DJFliX/OakPowerBoard/code/oakpowerboard/roboto_10.h

#ifndef __ROBOTO_10_
#define __ROBOTO_10_

const char Roboto_Plain_10[] PROGMEM = {
  0x0A, // Width: 10
  0x0D, // Height: 13
  0x20, // First Char: 32
  0xE0, // Numbers of Chars: 224

  // Char Widths:
  0x02, // 32: 2
  0x03, // 33: 3
  0x04, // 34: 4
  0x06, // 35: 6
  0x07, // 36: 7
  0x09, // 37: 9
  0x07, // 38: 7
  0x03, // 39: 3
  0x04, // 40: 4
  0x04, // 41: 4
  0x05, // 42: 5
  0x05, // 43: 5
  0x03, // 44: 3
  0x03, // 45: 3
  0x03, // 46: 3
  0x04, // 47: 4
  0x07, // 48: 7
  0x06, // 49: 6
  0x06, // 50: 6
  0x06, // 51: 6
  0x06, // 52: 6
  0x06, // 53: 6
  0x07, // 54: 7
  0x06, // 55: 6
  0x06, // 56: 6
  0x07, // 57: 7
  0x02, // 58: 2
  0x03, // 59: 3
  0x06, // 60: 6
  0x05, // 61: 5
  0x06, // 62: 6
  0x06, // 63: 6
  0x0A, // 64: 10
  0x07, // 65: 7
  0x07, // 66: 7
  0x07, // 67: 7
  0x07, // 68: 7
  0x06, // 69: 6
  0x06, // 70: 6
  0x08, // 71: 8
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

  // Font Data:
  0x00,0x00,0x00,0x00, // 32
  0x80,0x24,0x09,0x10,0x00, // 33
  0x00,0x66,0x00,0x00,0x00,0x00,0x00, // 34
  0x00,0x40,0x51,0x3E,0x45,0xF9,0x8A,0x02,0x00,0x00, // 35
  0x00,0x04,0x47,0x24,0x22,0x60,0x40,0x22,0x0E,0x02,0x00,0x00, // 36
  0x00,0x00,0x38,0x50,0xA1,0xC2,0x03,0x1A,0x4C,0x94,0xC0,0x00,0x00,0x00,0x00, // 37
  0x00,0x00,0x87,0x42,0x61,0x30,0x64,0x12,0x1E,0x00,0x00,0x00, // 38
  0x80,0x04,0x00,0x00,0x00, // 39
  0x80,0x24,0x22,0x22,0x22,0x44,0x08, // 40
  0x10,0x22,0x44,0x44,0x44,0x22,0x01, // 41
  0x00,0x90,0xE2,0x14,0x02,0x00,0x00,0x00,0x00, // 42
  0x00,0x00,0x42,0xC8,0x27,0x04,0x00,0x00,0x00, // 43
  0x00,0x00,0x00,0x90,0x00, // 44
  0x00,0x00,0x1C,0x00,0x00, // 45
  0x00,0x00,0x00,0x10,0x00, // 46
  0x00,0x48,0x44,0x22,0x12,0x01,0x00, // 47
  0x00,0x00,0x47,0x24,0x12,0x89,0x44,0x22,0x0E,0x00,0x00,0x00, // 48
  0x00,0x80,0x38,0x08,0x82,0x20,0x08,0x02,0x00,0x00, // 49
  0x00,0xC0,0x48,0x12,0x84,0x10,0x86,0x07,0x00,0x00, // 50
  0x00,0xC0,0x48,0x10,0x03,0x41,0x12,0x03,0x00,0x00, // 51
  0x00,0x00,0x61,0x14,0x25,0xF9,0x10,0x04,0x00,0x00, // 52
  0x00,0xE0,0x09,0x82,0x03,0x41,0x92,0x03,0x00,0x00, // 53
  0x00,0x00,0x86,0x20,0xF0,0x88,0x44,0x22,0x0E,0x00,0x00,0x00, // 54
  0x00,0xF0,0x41,0x08,0x42,0x10,0x84,0x00,0x00,0x00, // 55
  0x00,0xC0,0x48,0x12,0x23,0x49,0x12,0x03,0x00,0x00, // 56
  0x00,0x00,0x47,0x24,0x12,0xF1,0x40,0x10,0x06,0x00,0x00,0x00, // 57
  0x00,0x02,0x08,0x00, // 58
  0x00,0x20,0x00,0x92,0x00, // 59
  0x00,0x00,0x00,0x10,0x23,0x30,0x10,0x00,0x00,0x00, // 60
  0x00,0x00,0x00,0x3C,0xF0,0x00,0x00,0x00,0x00, // 61
  0x00,0x00,0x00,0x02,0x03,0x31,0x02,0x00,0x00,0x00, // 62
  0x00,0xE0,0x48,0x10,0xC6,0x10,0x00,0x01,0x00,0x00, // 63
  0x00,0x00,0x80,0x07,0x21,0x34,0xA9,0xA4,0x92,0x4A,0x2A,0x69,0x43,0x00,0x0E,0x00,0x00, // 64
  0x00,0x00,0x82,0x41,0xA1,0x48,0x7C,0xA2,0x10,0x00,0x00,0x00, // 65
  0x00,0x80,0x47,0x24,0xF2,0x88,0x44,0x22,0x0F,0x00,0x00,0x00, // 66
  0x00,0x00,0xC7,0x24,0x14,0x08,0x84,0x26,0x0E,0x00,0x00,0x00, // 67
  0x00,0x80,0x47,0x22,0x12,0x89,0x44,0x12,0x0F,0x00,0x00,0x00, // 68
  0x00,0xE0,0x0B,0x82,0x27,0x08,0x82,0x0F,0x00,0x00, // 69
  0x00,0xE0,0x09,0x82,0xE0,0x09,0x82,0x00,0x00,0x00, // 70
  0x00,0x00,0x3C,0x66,0x02,0x02,0x72,0x42,0x44,0x3C,0x00,0x00,0x00,0x00, // 71
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
};

#endif
