DJFliX/OakPowerBoard/code/oakpowerboard/roboto_thin_20.h

#ifndef __ROBOTO_20_
#define __ROBOTO_20_

const char Roboto_Thin_Plain_20[] PROGMEM = {
  0x13, // Width: 19
  0x18, // Height: 24
  0x20, // First Char: 32
  0xE0, // Numbers of Chars: 224

  // Char Widths:
  0x05, // 32: 5
  0x03, // 33: 3
  0x05, // 34: 5
  0x0B, // 35: 11
  0x0B, // 36: 11
  0x0F, // 37: 15
  0x0C, // 38: 12
  0x03, // 39: 3
  0x06, // 40: 6
  0x06, // 41: 6
  0x09, // 42: 9
  0x0B, // 43: 11
  0x03, // 44: 3
  0x06, // 45: 6
  0x04, // 46: 4
  0x08, // 47: 8
  0x0B, // 48: 11
  0x0B, // 49: 11
  0x0B, // 50: 11
  0x0B, // 51: 11
  0x0C, // 52: 12
  0x0B, // 53: 11
  0x0B, // 54: 11
  0x0B, // 55: 11
  0x0C, // 56: 12
  0x0B, // 57: 11
  0x04, // 58: 4
  0x03, // 59: 3
  0x0A, // 60: 10
  0x0B, // 61: 11
  0x0A, // 62: 10
  0x09, // 63: 9
  0x13, // 64: 19
  0x0C, // 65: 12
  0x0D, // 66: 13
  0x0D, // 67: 13
  0x0D, // 68: 13
  0x0C, // 69: 12
  0x0C, // 70: 12
  0x0E, // 71: 14
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

  // Font Data:
  0x00,0x00,0x00,0x00,0x00,0x00,0x00,0x00,0x00,0x00,0x00,0x00,0x00,0x00,0x00,0x00, // 32
  0x00,0x20,0x49,0x92,0x24,0x09,0x80,0x00,0x00,0x00, // 33
  0x00,0x00,0xA0,0x94,0x52,0x00,0x00,0x00,0x00,0x00,0x00,0x00,0x00,0x00,0x00,0x00, // 34
  0x00,0x00,0x00,0x00,0x00,0x00,0x21,0x88,0x40,0x04,0x22,0xFE,0x87,0x08,0x42,0x10,0x81,0x08,0x44,0xFC,0x1F,0x11,0x84,0x20,0x02,0x11,0x00,0x00,0x00,0x00,0x00,0x00,0x00,0x00, // 35
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
  0x00,0x00,0x00,0x00,0x00,0x00,0x00,0xF0,0x01,0x82,0x41,0x40,0x08,0x20,0x02,0x80,0x00,0x20,0x00,0x08,0x00,0x82,0x8F,0x00,0x22,0x80,0x08,0x20,0x04,0x08,0x02,0x02,0x7F,0x00,0x00,0x00,0x00,0x00,0x00,0x00,0x00,0x00,0x00, // 71
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
};
#endif
