DJFliX/OakPowerBoard/code/oakpowerboard/roboto_12.h

const char Roboto_Plain_12[] PROGMEM = {
  0x0C, // Width: 12
  0x0F, // Height: 15
  0x20, // First Char: 32
  0xE0, // Numbers of Chars: 224

  // Char Widths:
  0x03, // 32: 3
  0x03, // 33: 3
  0x04, // 34: 4
  0x07, // 35: 7
  0x07, // 36: 7
  0x0A, // 37: 10
  0x08, // 38: 8
  0x03, // 39: 3
  0x04, // 40: 4
  0x04, // 41: 4
  0x05, // 42: 5
  0x08, // 43: 8
  0x03, // 44: 3
  0x03, // 45: 3
  0x03, // 46: 3
  0x05, // 47: 5
  0x07, // 48: 7
  0x06, // 49: 6
  0x07, // 50: 7
  0x07, // 51: 7
  0x07, // 52: 7
  0x07, // 53: 7
  0x07, // 54: 7
  0x07, // 55: 7
  0x07, // 56: 7
  0x07, // 57: 7
  0x03, // 58: 3
  0x03, // 59: 3
  0x07, // 60: 7
  0x07, // 61: 7
  0x07, // 62: 7
  0x06, // 63: 6
  0x0C, // 64: 12
  0x08, // 65: 8
  0x08, // 66: 8
  0x08, // 67: 8
  0x08, // 68: 8
  0x07, // 69: 7
  0x07, // 70: 7
  0x09, // 71: 9
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

  // Font Data:
  0x00,0x00,0x00,0x00,0x00,0x00, // 32
  0x00,0x24,0x49,0x02,0x04,0x00, // 33
  0x00,0x66,0x06,0x00,0x00,0x00,0x00,0x00, // 34
  0x00,0x00,0x00,0x85,0xF2,0x93,0x48,0x7E,0x0A,0x85,0x02,0x00,0x00,0x00, // 35
  0x00,0x04,0x47,0x26,0x12,0x30,0x30,0x20,0x91,0x88,0x83,0x00,0x00,0x00, // 36
  0x00,0x00,0x00,0x00,0x03,0x52,0x48,0xC1,0x02,0x04,0xD0,0xA0,0x84,0x12,0x30,0x00,0x00,0x00,0x00, // 37
  0x00,0x00,0x00,0x18,0x24,0x24,0x1C,0x0C,0x52,0x62,0x22,0x7C,0x00,0x00,0x00,0x00, // 38
  0x80,0x24,0x00,0x00,0x00,0x00, // 39
  0x00,0x48,0x24,0x22,0x22,0x22,0x44,0x08, // 40
  0x00,0x21,0x42,0x44,0x44,0x44,0x22,0x01, // 41
  0x00,0x00,0x42,0xBE,0x51,0x00,0x00,0x00,0x00,0x00, // 42
  0x00,0x00,0x00,0x00,0x08,0x08,0x08,0x7E,0x08,0x08,0x08,0x00,0x00,0x00,0x00,0x00, // 43
  0x00,0x00,0x00,0x00,0x24,0x01, // 44
  0x00,0x00,0x00,0x07,0x00,0x00, // 45
  0x00,0x00,0x00,0x00,0x04,0x00, // 46
  0x00,0x00,0x84,0x10,0x21,0x44,0x08,0x11,0x00,0x00, // 47
  0x00,0x00,0x80,0x23,0x13,0x89,0x44,0x22,0x91,0x8C,0x03,0x00,0x00,0x00, // 48
  0x00,0x00,0x20,0x0E,0x82,0x20,0x08,0x82,0x20,0x00,0x00,0x00, // 49
  0x00,0x00,0x80,0x23,0x12,0x81,0x20,0x08,0x06,0xC1,0x07,0x00,0x00,0x00, // 50
  0x00,0x00,0x80,0x23,0x02,0x81,0x30,0x20,0x90,0x88,0x03,0x00,0x00,0x00, // 51
  0x00,0x00,0x00,0x04,0x43,0xA1,0x48,0x26,0x3F,0x08,0x04,0x00,0x00,0x00, // 52
  0x00,0x00,0xC0,0x27,0x10,0x78,0x60,0x20,0x91,0x88,0x03,0x00,0x00,0x00, // 53
  0x00,0x00,0x00,0x43,0x10,0x78,0x44,0x22,0x91,0x89,0x03,0x00,0x00,0x00, // 54
  0x00,0x00,0xE0,0x07,0x82,0x40,0x10,0x08,0x06,0x81,0x00,0x00,0x00,0x00, // 55
  0x00,0x00,0x80,0x23,0x12,0x89,0x38,0x22,0x91,0x88,0x03,0x00,0x00,0x00, // 56
  0x00,0x00,0x80,0x23,0x13,0x89,0x44,0x3C,0x10,0x84,0x01,0x00,0x00,0x00, // 57
  0x00,0x00,0x01,0x00,0x04,0x00, // 58
  0x00,0x00,0x01,0x80,0x24,0x00, // 59
  0x00,0x00,0x00,0x00,0x00,0x61,0x0C,0x0E,0x1C,0x08,0x00,0x00,0x00,0x00, // 60
  0x00,0x00,0x00,0x00,0xF0,0x01,0x00,0x3E,0x00,0x00,0x00,0x00,0x00,0x00, // 61
  0x00,0x00,0x00,0x00,0x10,0x30,0x60,0x38,0x87,0x00,0x00,0x00,0x00,0x00, // 62
  0x00,0x00,0x38,0x12,0x04,0x21,0x04,0x01,0x10,0x00,0x00,0x00, // 63
  0x00,0x00,0x00,0x00,0x00,0x0F,0x08,0x43,0x20,0xE2,0x24,0x49,0x92,0x24,0x49,0xD2,0x26,0x3B,0x04,0xC0,0x00,0xF0,0x00, // 64
  0x00,0x00,0x00,0x18,0x18,0x18,0x24,0x24,0x26,0x7E,0x42,0x43,0x00,0x00,0x00,0x00, // 65
  0x00,0x00,0x00,0x3E,0x42,0x42,0x42,0x3E,0x42,0x42,0x42,0x3E,0x00,0x00,0x00,0x00, // 66
  0x00,0x00,0x00,0x38,0x44,0x42,0x02,0x02,0x02,0x42,0x44,0x38,0x00,0x00,0x00,0x00, // 67
  0x00,0x00,0x00,0x1E,0x22,0x42,0x42,0x42,0x42,0x42,0x22,0x1E,0x00,0x00,0x00,0x00, // 68
  0x00,0x00,0xC0,0x27,0x10,0x08,0x7C,0x02,0x81,0xC0,0x07,0x00,0x00,0x00, // 69
  0x00,0x00,0xC0,0x27,0x10,0x08,0x7C,0x02,0x81,0x40,0x00,0x00,0x00,0x00, // 70
  0x00,0x00,0x00,0xC0,0x43,0x4C,0x80,0x00,0x71,0x82,0x04,0x11,0xC2,0x03,0x00,0x00,0x00, // 71
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
};
