DJFliX/OakPowerBoard/code/oakpowerboard/images.h

const char activeSymbole[] PROGMEM = {
    B00000000,
    B00011000,
    B00100100,
    B01011010,
    B01011010,
    B00100100,
    B00011000,
    B00000000,
};

const char inactiveSymbole[] PROGMEM = {
    B00000000,
    B00000000,
    B00000000,
    B00011000,
    B00011000,
    B00000000,
    B00000000,
    B00000000,
};

const char wifiActive[] PROGMEM = {
    B00111100,
    B01000010,
    B10011001,
    B00100100,
    B00000000,
    B00011000,
    B00011000,
    B00000000
};

const char wifiInactive[] PROGMEM = {
    B00000000,
    B00000000,
    B00000000,
    B00000000,
    B00000000,
    B00011000,
    B00011000,
    B00000000
};
